LeftyDeMilo/clock-pulse-generator/clock_pulse_generator/globals.h

#ifndef GLOBALS_H
#define GLOBALS_H

#include <Arduino.h>
#include "symbolSevenSegmentFont.h"

#define ANIMATION_MODE true

// Common terminal aliases
#define ANODE HIGH
#define CATHODE LOW

bool buttonPressed = false;

#endif
